LeoDeLaFuente/Slam_Arduino_Bot/documentation/Diagramme_de_Gantt.png

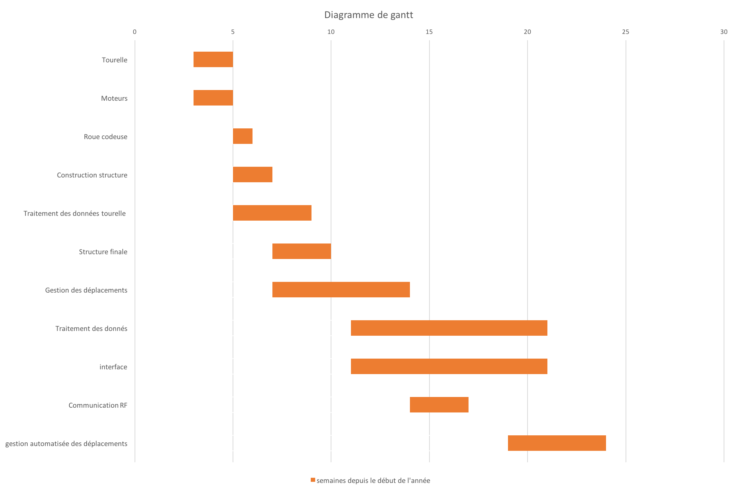
documentation/Diagramme_de_Gantt.png
