LeoDeLaFuente/Slam_Arduino_Bot/documentation/gantt2.png

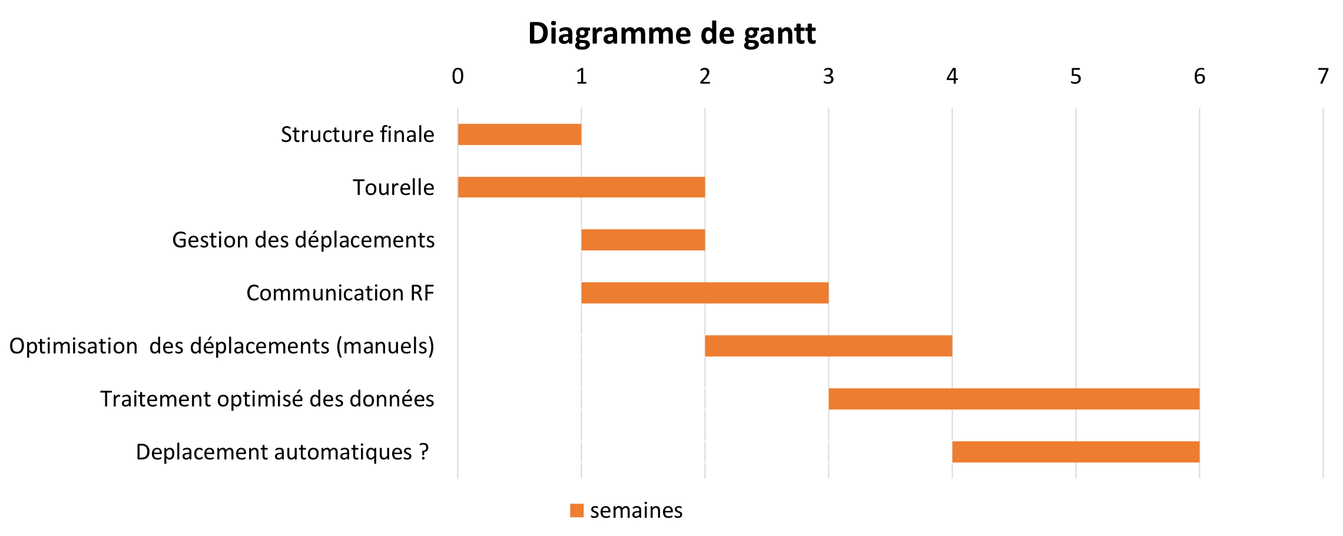
documentation/gantt2.png
