LeoDeLaFuente/Slam_Arduino_Bot/documentation/Images/41UWAjamQIL._SX355_.jpg

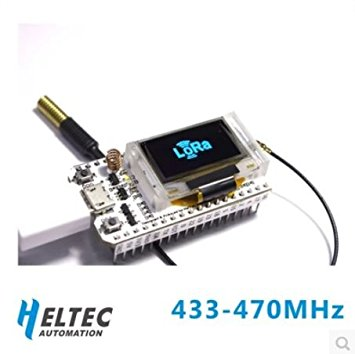
documentation/Images/41UWAjamQIL._SX355_.jpg
