LeoDeLaFuente/Slam_Arduino_Bot/documentation/Images/30074633_1792023070850157_102525186_o.jpg

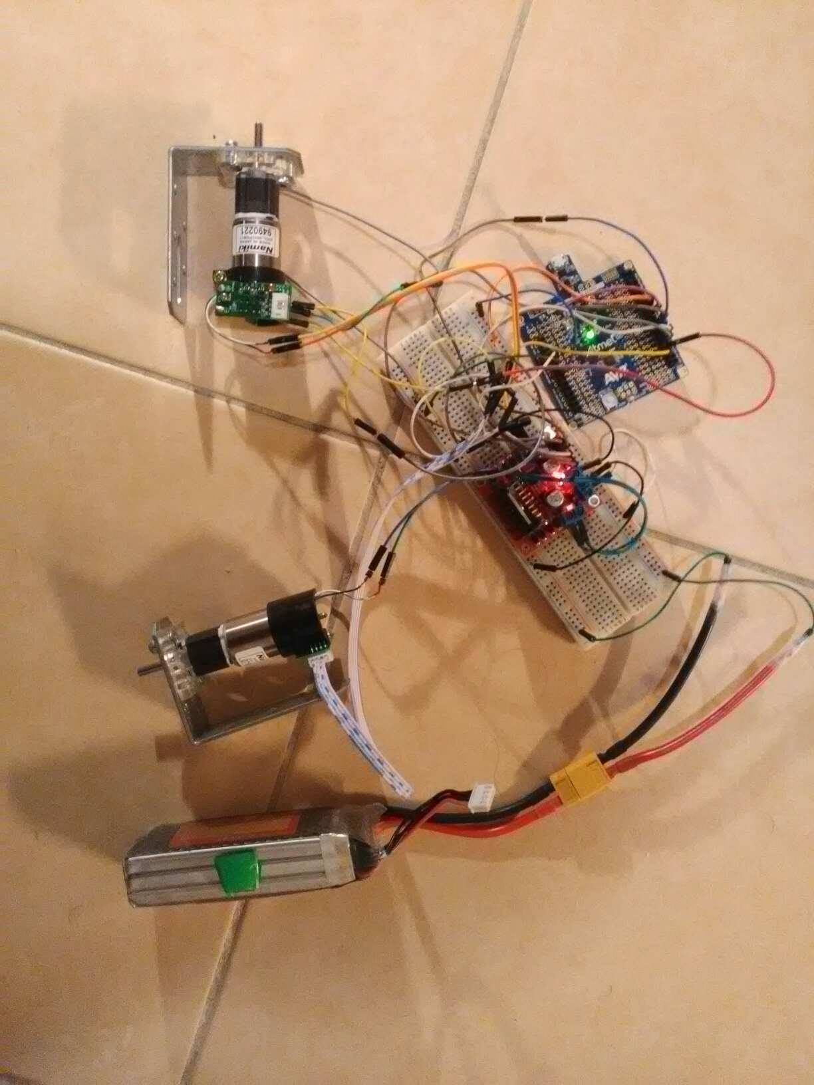
documentation/Images/30074633_1792023070850157_102525186_o.jpg
