LeoDeLaFuente/Slam_Arduino_Bot/documentation/Images/cablage_laser.jpg

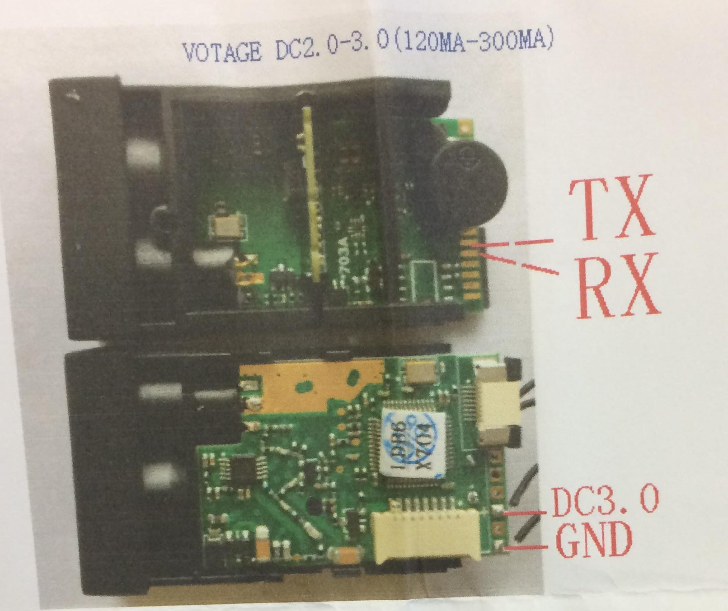
documentation/Images/cablage_laser.jpg
