LeoDeLaFuente/Slam_Arduino_Bot/documentation/Images/esp.jpg

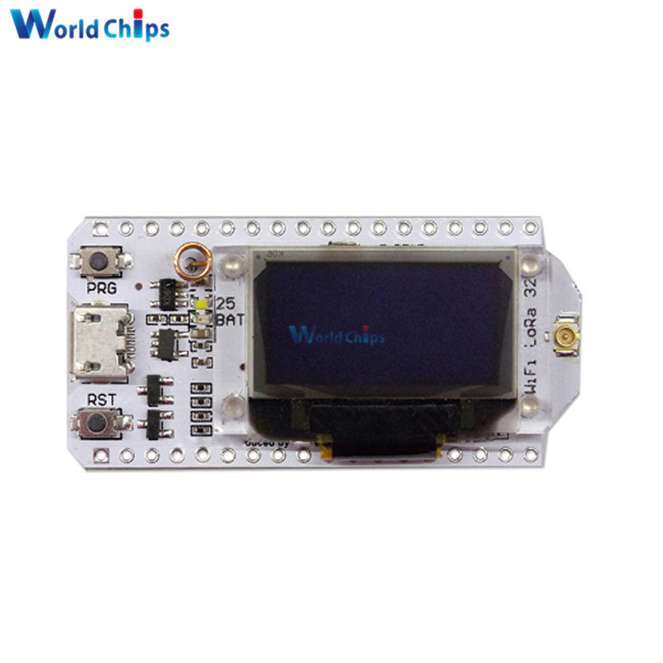
documentation/Images/esp.jpg
