LeoDeLaFuente/Slam_Arduino_Bot/documentation/Images/IMG_1142.jpg

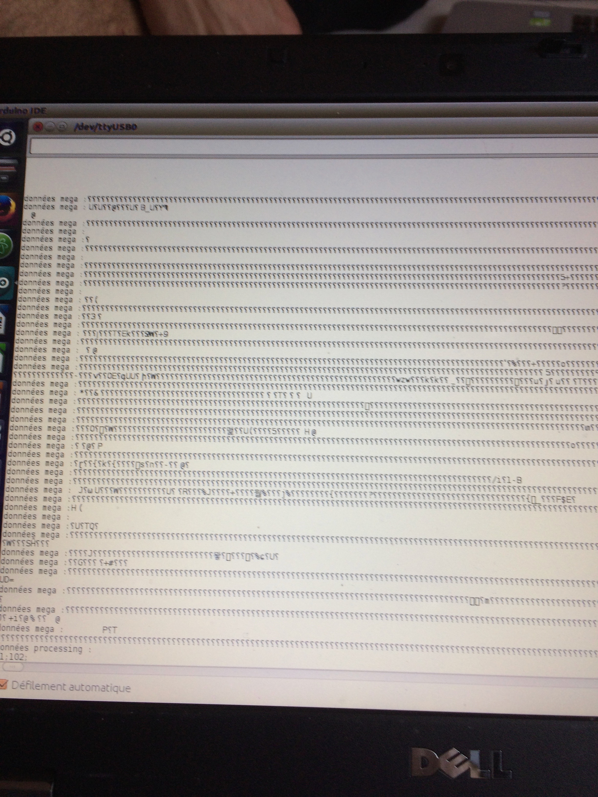
documentation/Images/IMG_1142.jpg
