LeoDeLaFuente/Slam_Arduino_Bot/documentation/Images/microLidar.jpg

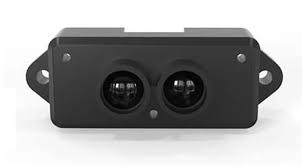
documentation/Images/microLidar.jpg
