LeoDeLaFuente/Slam_Arduino_Bot/documentation/Images/Moteur.JPG

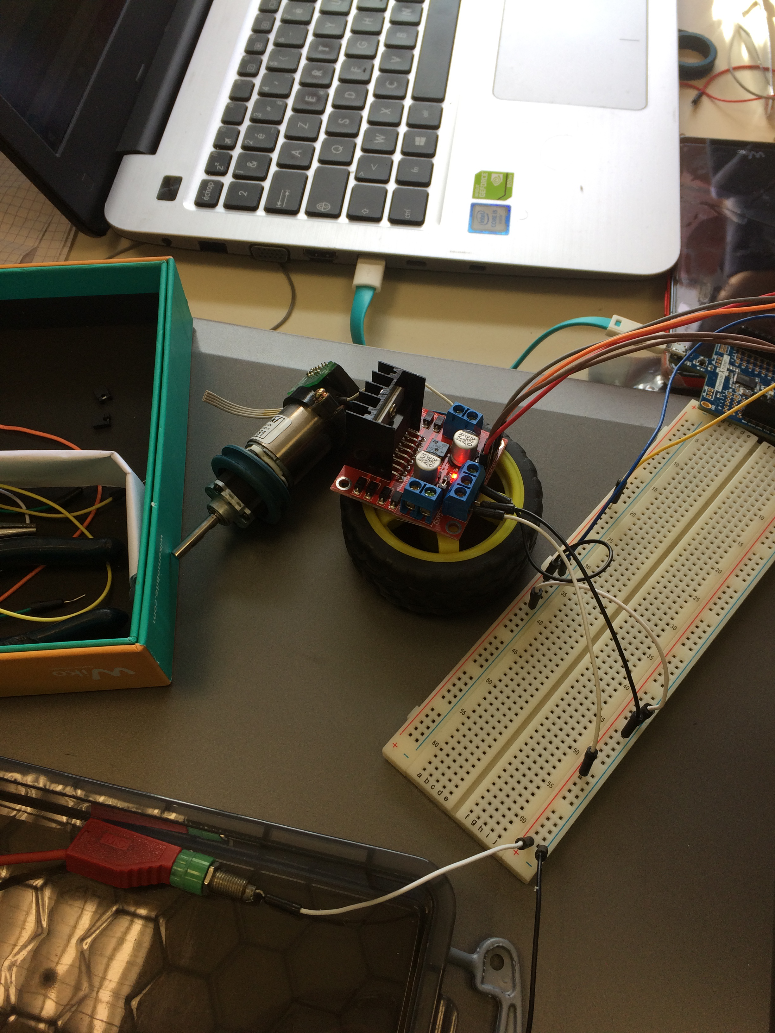
documentation/Images/Moteur.JPG
