LeoDeLaFuente/Slam_Arduino_Bot/documentation/Images/piles.jpg

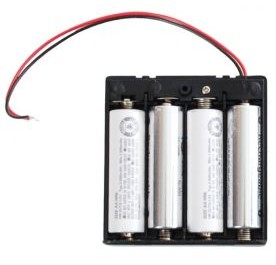
documentation/Images/piles.jpg
