LeoDeLaFuente/Slam_Arduino_Bot/documentation/Images/schéma_ordi.jpg

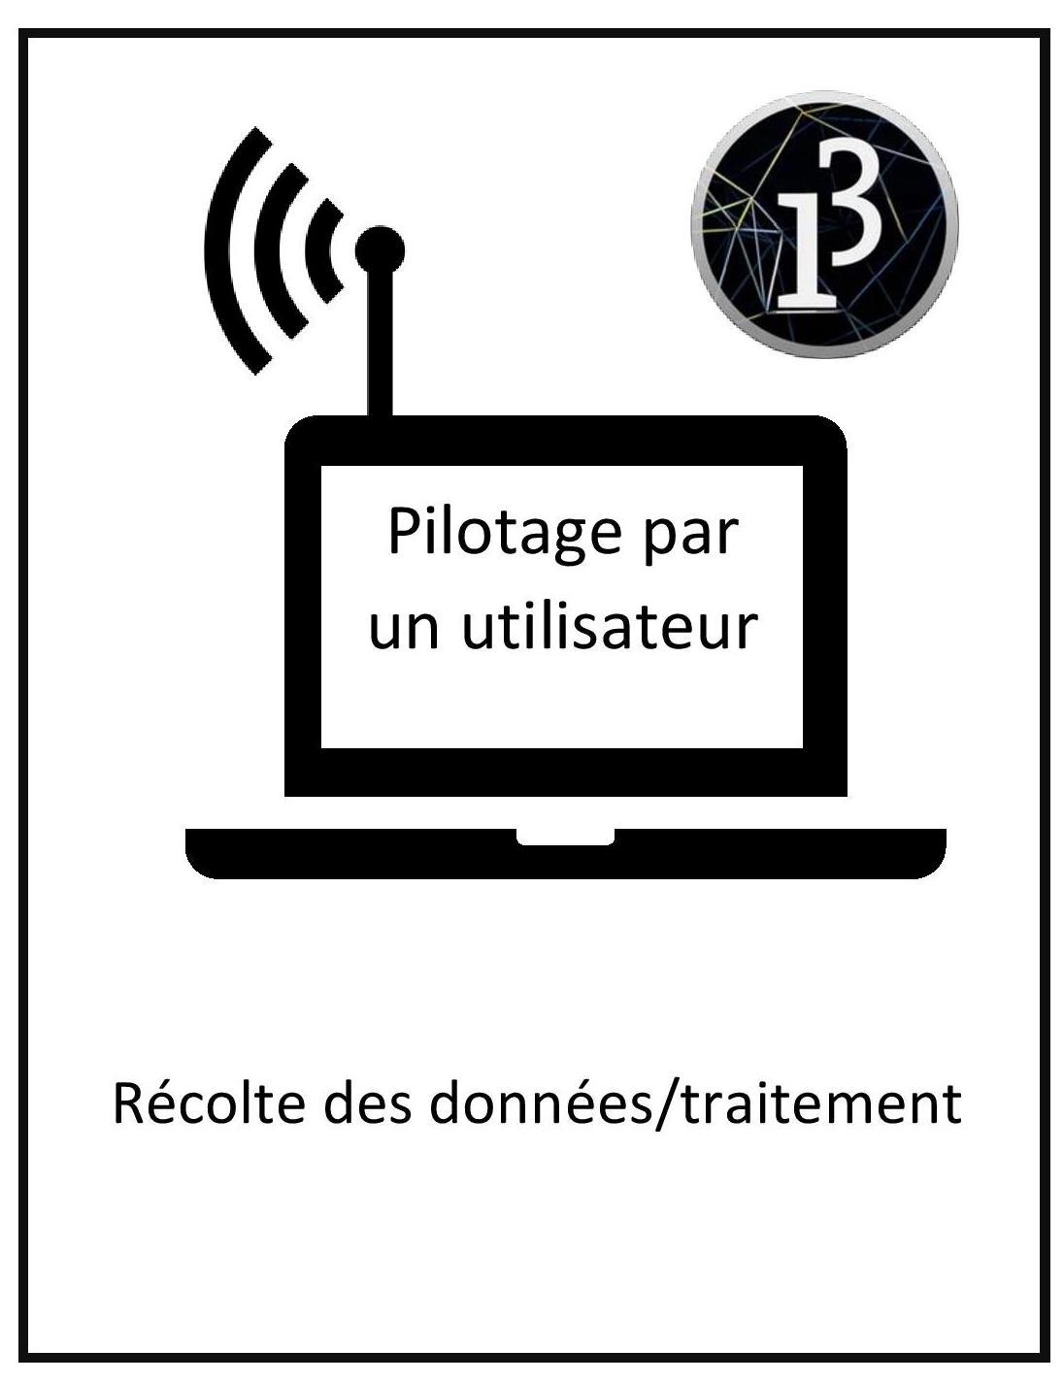
documentation/Images/schéma_ordi.jpg
