LeoDeLaFuente/Slam_Arduino_Bot/documentation/Images/schéma_robot.jpg

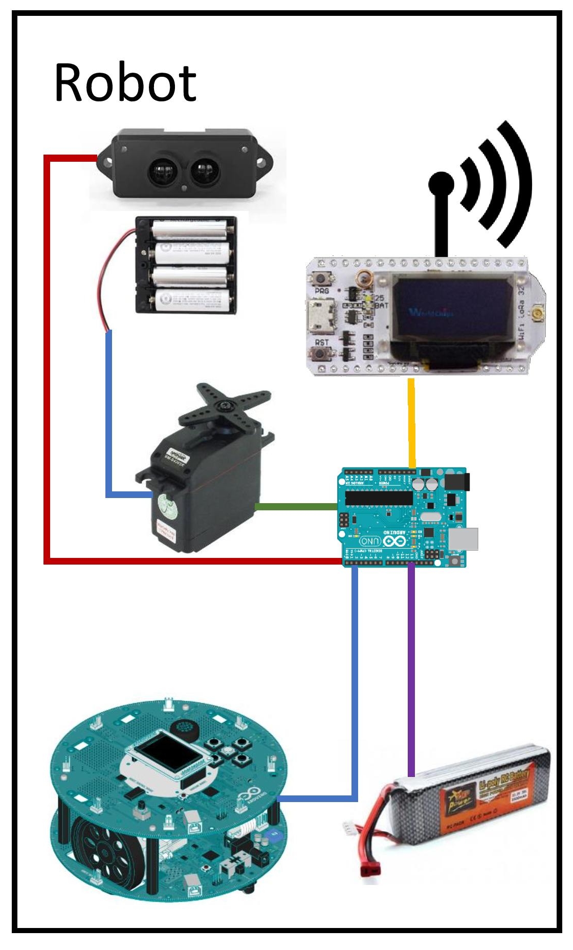
documentation/Images/schéma_robot.jpg
