LeoDeLaFuente/Slam_Arduino_Bot/documentation/Images/Schéma_wifi_v2.jpg

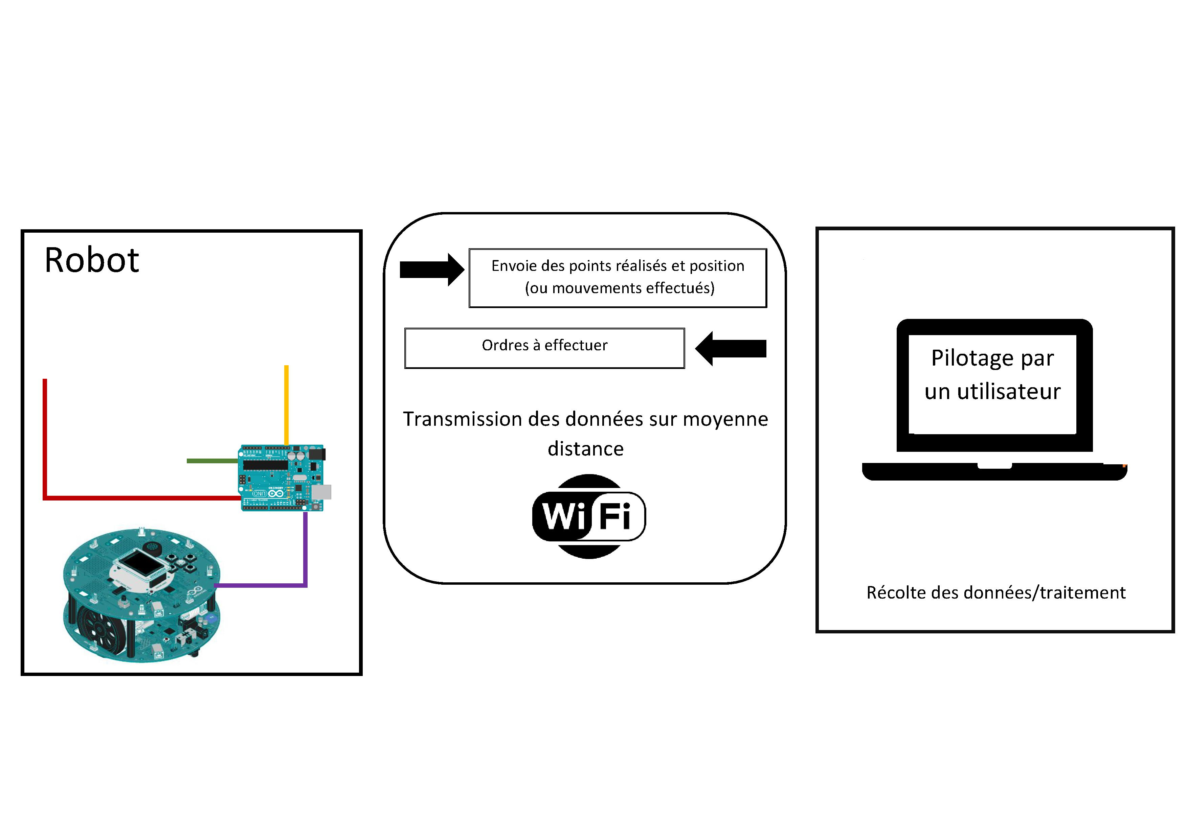
documentation/Images/Schéma_wifi_v2.jpg
