LeoDeLaFuente/Slam_Arduino_Bot/code/code_esp32/code_esp32.ino

/*
  * Exemple de code de l'esp32 communiquant avec un server processing sur le même réseau.
*/



#include <SPI.h>
#include <LoRa.h>
#include <WiFi.h>
#include <Wire.h>
#include "SSD1306.h"
#include <SoftwareSerial.h>


const char* ssid     = "Le nom de votre réseau";
const char* password = "Le mot de passe";

const char* ssidProcessing = "L'adresse ip de processing";

const int port = 8080;

int distance = 0;
int angle = 0;

SoftwareSerial portEsp(17,16); // RX = 17 | Tx = 16


WiFiClient servProcessing;


//écran oled//
SSD1306 display(0x3c, 4, 15);



void setup(){
/*==== initialisation de l'écran ====*/
    pinMode(25,OUTPUT);
    pinMode(16,OUTPUT);
    digitalWrite(16, LOW);    // set GPIO16 low to reset OLED
    delay(50);
    digitalWrite(16, HIGH); // while OLED is running, must set GPIO16 in high
    display.init();
    display.flipScreenVertically();
    display.setFont(ArialMT_Plain_10);
    display.clear();
/*==================*/

    portEsp.begin(115200);

    Serial.begin(115200);
    delay(100);

    // We start by connecting to a WiFi network

    Serial.println();
    Serial.println();
    display.drawString(0, 0,"Connecting to "+String(ssid));
    display.display();
    Serial.print("Connecting to ");
    Serial.println(ssid);

    WiFi.begin(ssid, password);
    //WiFi.begin(ssid1);
    while (WiFi.status() != WL_CONNECTED) {
        delay(50);
        Serial.print(".");
        display.drawString(10,0,"...");
        display.display();
        delay(250);
        display.clear();
    }

    display.clear();
    display.drawString(0,0,"WiFi connected");
    display.drawString(0,10,"IP address: ");
    display.drawString(0,20,String(WiFi.localIP()));
    display.display();

    Serial.println("");
    Serial.println("WiFi connected");
    Serial.println("IP address: ");
    Serial.println(WiFi.localIP());
    delay(300);

    //=== début de la connexion vers le server processing ===//

    display.clear();
    display.drawString(0,0,"connecting to "+String(ssidProcessing));
    display.display();
    Serial.print("connecting to ");
    Serial.println(ssidProcessing);

    // Use WiFiClient class to create TCP connections
    connexion();
}


void loop(){


    portEsp.listen();

    String envoi = "";
    while ( portEsp.available() > 0){
      envoi += portEsp.read()

    }

    ecrire(envoi);
    //unsigned long t1 = millis();
    String envoi = "::"+String(distance)+";"+String(angle)+";instruction\r";
    servProcessing.print(envoi);
    unsigned long timeout = millis();
    if(servProcessing.available()) lireServ();
    delay(3);
    distance += 7;
    angle ++;
    if(distance >= 1000) distance = 0;
    if(angle == 200) angle = 0;

}

void lireServ(){
  while(servProcessing.available()) {
        String line = servProcessing.readStringUntil('\r');
        ecrire(line);
  }
}

void connexion(){
      if (!servProcessing.connect(ssidProcessing, port)) {
        ecrire("connexion fail");
        connexion();
        return;
    }


    //ici on envoie des données à processing
    servProcessing.print("début de la communication avec esp32\r");
    unsigned long timeout = millis();
    while (servProcessing.available() == 0) {
        if (millis() - timeout > 5000) {
            ecrire(">>> servProcessing Timeout !");
            servProcessing.stop();
            return;
        }
    }

    // Read all the lines of the reply from server and print them to Serial
    while(servProcessing.available()) {
        String line = servProcessing.readStringUntil('\r');
        //Serial.print(line);
        ecrire(line);
    }
}

void ecrire(String s){
  Serial.println(s);
  display.clear();
  display.drawString(0,0,s);
  display.display();
}
