LeoDeLaFuente/Slam_Arduino_Bot/code/bin/autres_codes_arduino/test_Simpletimer/test_Simpletimer.ino

#include <SimpleTimer.h>

// the timer object
SimpleTimer timer;

// a function to be executed periodically
void repeatMe() {
    Serial.print("Uptime (s): ");
    Serial.println(millis() / 1000);
}

void setup() {
    Serial.begin(9600);
    timer.setInterval(1000, repeatMe);
}

void loop() {
    timer.run();
}
